evezor/v0_servox16_board/pics/20201126_045630.jpg

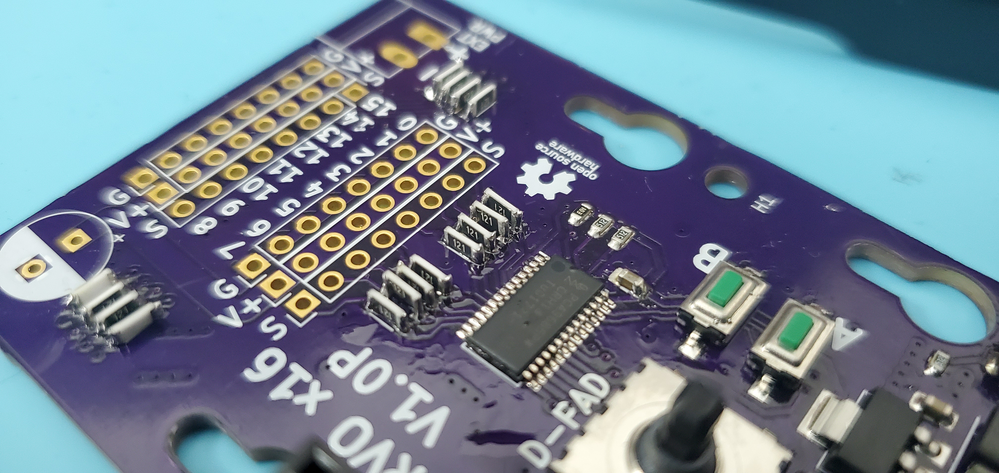
pics/20201126_045630.jpg
