evezor/v0_servox16_board/pics/20201126_050736.jpg

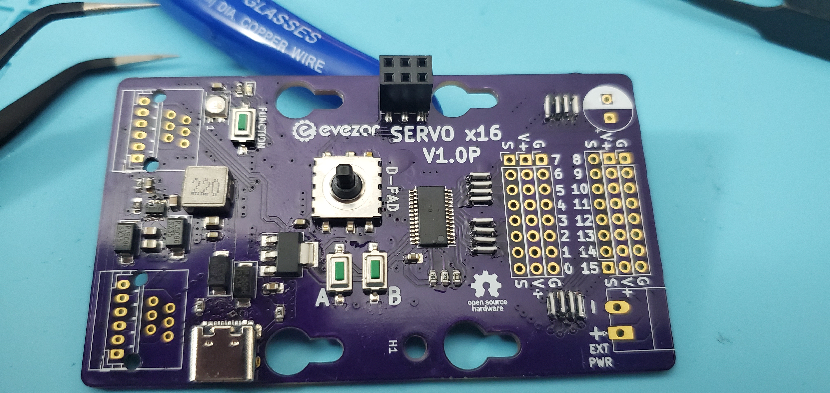
pics/20201126_050736.jpg
