evezor/v0_servox16_board/pics/20201202_075417.jpg

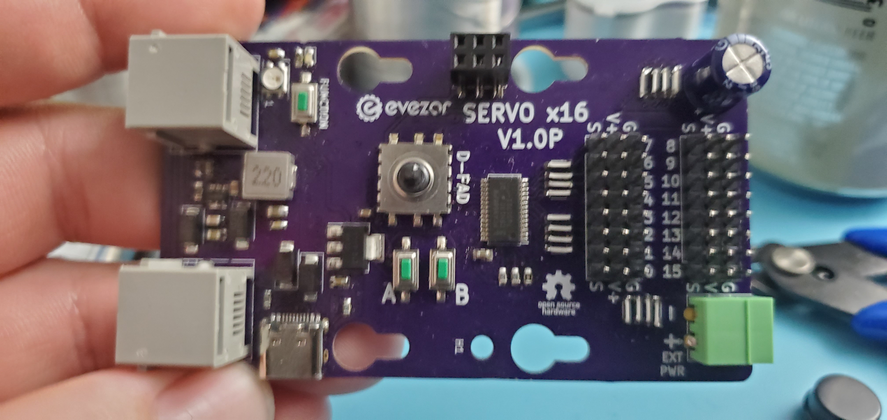
pics/20201202_075417.jpg
